timothy-fuchs/basilisk-hatchling/media/don_t_do_this.png

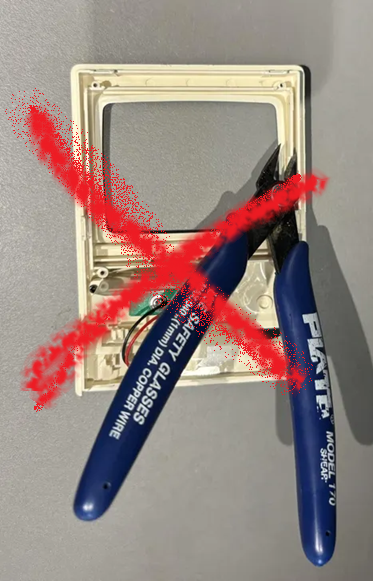
media/don_t_do_this.png
